RajanaKavinda/Smart-LPG-Gas-Leakage-Detecter-EN2160/Photos and Videos/IMG_20230722_174817.jpg

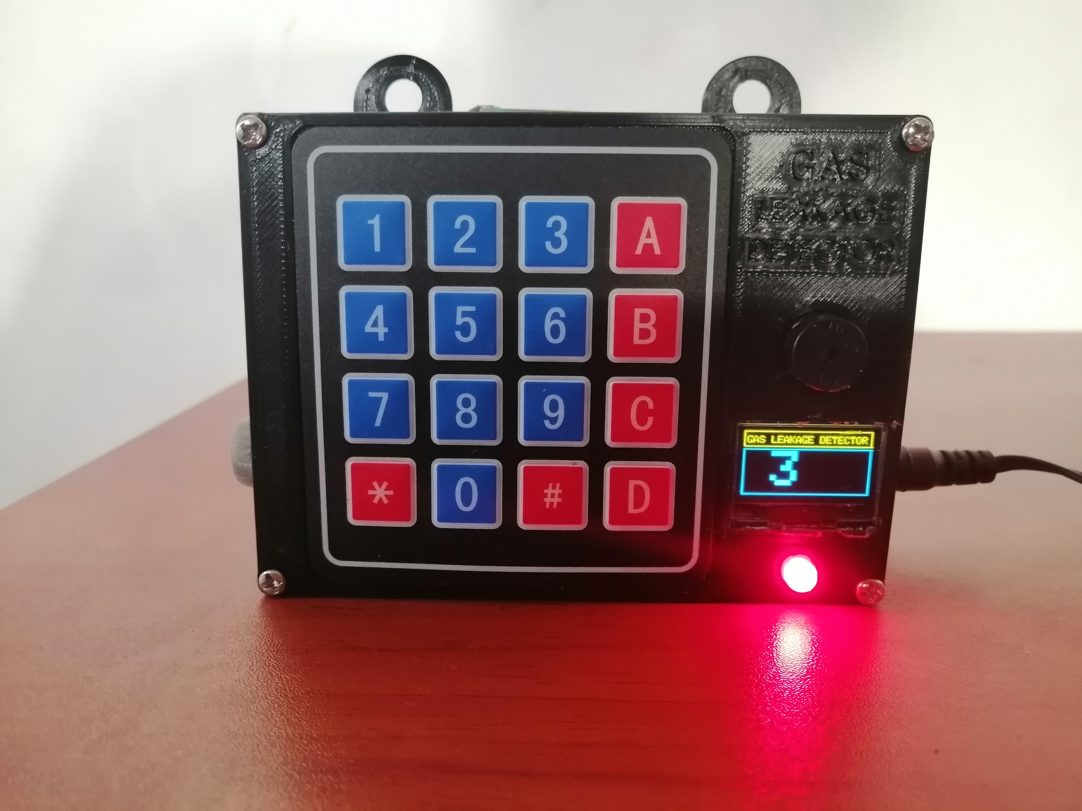
Photos and Videos/IMG_20230722_174817.jpg
