RajanaKavinda/Smart-LPG-Gas-Leakage-Detecter-EN2160/Photos and Videos/IMG_20230722_180356.jpg

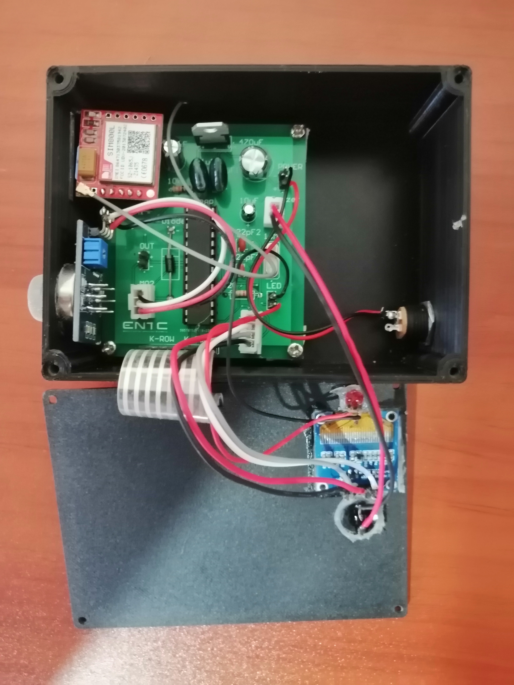
Photos and Videos/IMG_20230722_180356.jpg
