RajanaKavinda/Smart-LPG-Gas-Leakage-Detecter-EN2160/Photos and Videos/WhatsApp Image 2023-09-08 at 16.50.58.jpg

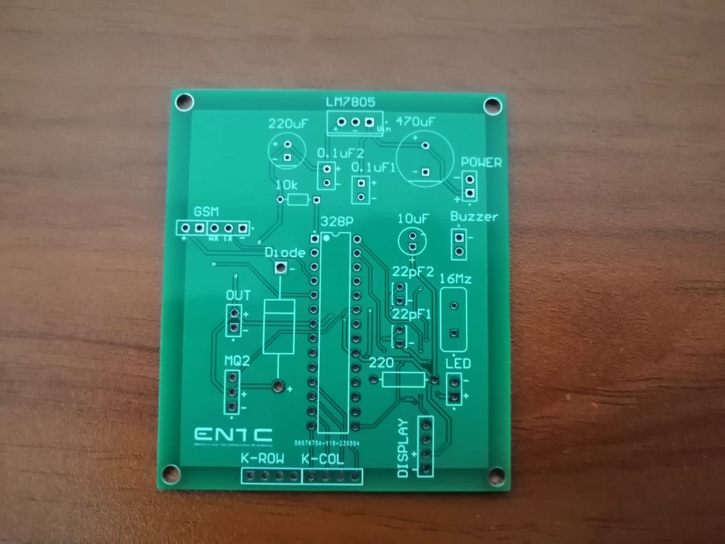
Photos and Videos/WhatsApp Image 2023-09-08 at 16.50.58.jpg
